grender007/Modular-Biomedical-Sensor-Board-for-Education/Skin Impedance Sensor/PCB/1326417348356.png

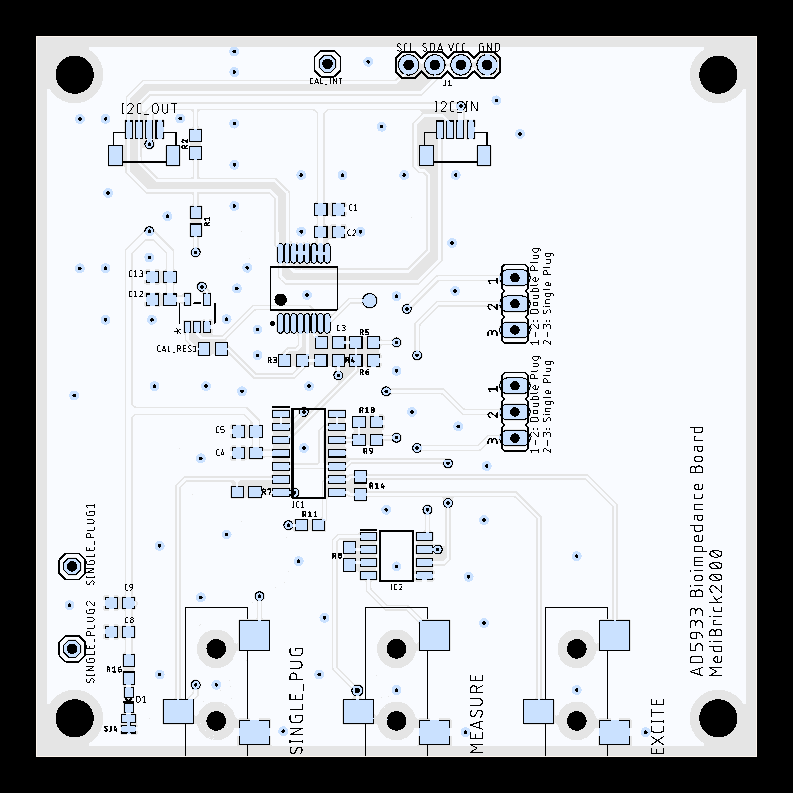
Skin Impedance Sensor/PCB/1326417348356.png
